Computationgeek/Microlab_16F/Schematic/PIC16FSCH.kicad_sch

## KiCad design Schematic/PIC16FSCH.kicad_sch (2026-04-24)

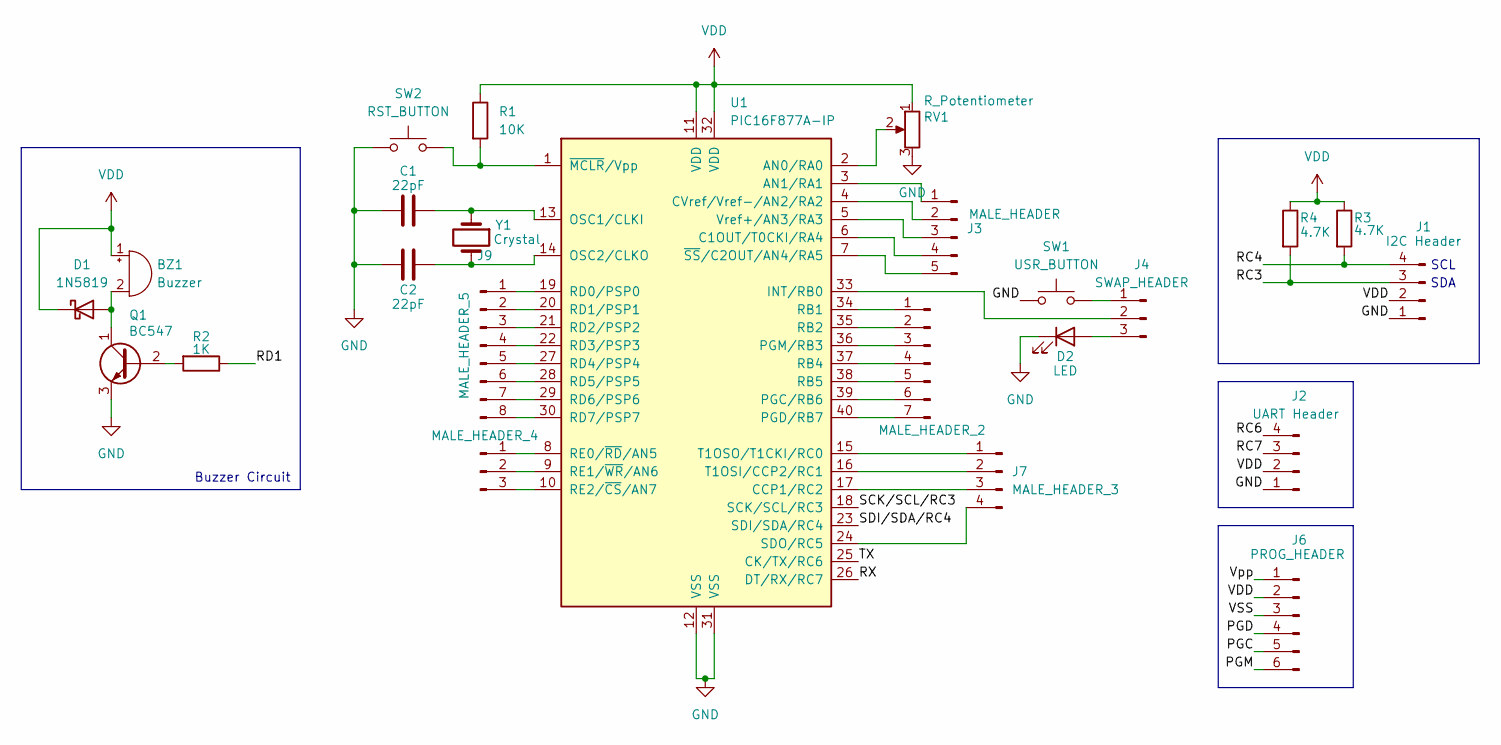
[picture p7: schematic PIC16FSCH.kicad_sch]

Parts:
BZ1: Buzzer
C1, C2: 22pF
D1: 1N5819; D_DO-41_SOD81_P10.16mm_Horizontal
D2: LED
J1: I2C Header
J2: UART Header
J3: MALE_HEADER
J4: SWAP_HEADER
J5: MALE_HEADER_2
J6: PROG_HEADER
J7: MALE_HEADER_3
J8: MALE_HEADER_4
J9: MALE_HEADER_5
Q1: BC547; TO-92_Inline
R1: 10K
R2: 1K
R3, R4: 4.7K
RV1: R_Potentiometer
SW1: USR_BUTTON
SW2: RST_BUTTON
U1: PIC16F877A-IP
Y1: Crystal

Connections:
GND: C1.2, C2.2, D2.1 (K), J1.1, J2.1, Q1.3 (E), RV1.3, SW1.1, SW2.1, U1.12 (VSS), U1.31 (VSS)
unnamed: BZ1.2 (-), D1.2 (A), Q1.1 (C)
unnamed: C1.1, U1.13 (OSC1/CLKI), Y1.1
unnamed: C2.1, U1.14 (OSC2/CLKO), Y1.2
unnamed: D2.2 (A), J4.3
unnamed: J3.1, U1.3 (AN1/RA1)
unnamed: J3.2, U1.4 (CVref/Vref-/AN2/RA2)
unnamed: J3.3, U1.5 (Vref+/AN3/RA3)
unnamed: J3.4, U1.6 (C1OUT/T0CKI/RA4)
unnamed: J3.5, U1.7 (~SS/C2OUT/AN4/RA5)
unnamed: J4.1, SW1.2
unnamed: J4.2, U1.33 (INT/RB0)
unnamed: J5.1, U1.34 (RB1)
unnamed: J5.2, U1.35 (RB2)
unnamed: J5.3, U1.36 (PGM/RB3)
unnamed: J5.4, U1.37 (RB4)
unnamed: J5.5, U1.38 (RB5)
unnamed: J5.6, U1.39 (PGC/RB6)
unnamed: J5.7, U1.40 (PGD/RB7)
unnamed: J7.1, U1.15 (T1OSO/T1CKI/RC0)
unnamed: J7.2, U1.16 (T1OSI/CCP2/RC1)
unnamed: J7.3, U1.17 (CCP1/RC2)
unnamed: J7.4, U1.24 (SDO/RC5)
unnamed: J8.1, U1.8 (RE0/~RD/AN5)
unnamed: J8.2, U1.9 (RE1/~WR/AN6)
unnamed: J8.3, U1.10 (RE2/~CS/AN7)
unnamed: J9.1, U1.19 (RD0/PSP0)
unnamed: J9.2, U1.20 (RD1/PSP1)
unnamed: J9.3, U1.21 (RD2/PSP2)
unnamed: J9.4, U1.22 (RD3/PSP3)
unnamed: J9.5, U1.27 (RD4/PSP4)
unnamed: J9.6, U1.28 (RD5/PSP5)
unnamed: J9.7, U1.29 (RD6/PSP6)
unnamed: J9.8, U1.30 (RD7/PSP7)
unnamed: Q1.2 (B), R2.2
unnamed: R1.2, SW2.2, U1.1 (~MCLR/Vpp)
unnamed: RV1.2, U1.2 (AN0/RA0)
PGC: J6.5
PGD: J6.4
PGM: J6.6
RC3: J1.3, R4.2
RC4: J1.4, R3.2
RC6: J2.4
RC7: J2.3
RD1: R2.1
RX: U1.26 (DT/RX/RC7)
SCK/SCL/RC3: U1.18 (SCK/SCL/RC3)
SDI/SDA/RC4: U1.23 (SDI/SDA/RC4)
TX: U1.25 (CK/TX/RC6)
VDD: BZ1.1 (+), D1.1 (K), J1.2, J2.2, J6.2, R1.1, R3.1, R4.1, RV1.1, U1.11 (VDD), U1.32 (VDD)
VSS: J6.3
Vpp: J6.1

Notes on the sheet:
SDA
Buzzer Circuit
SCL
